derrickthomin/DJBB-Midi-Loopster/src/debug.py

import time
from collections import OrderedDict
from settings import SETTINGS

DEBUG_INTERVAL_S = 1.5  # Interval to print debug info (seconds)
DEBUG_MODE = SETTINGS["DEBUG"]

class Debug():
    """
    Debugging utility for displaying and managing debug information.

    Attributes:
        debug_header (str): Header text for the debug information.
        debug_dict (OrderedDict): Ordered dictionary to store debug data.
        debug_timer (float): Timer for managing debug printing intervals.
    """

    def __init__(self):
        """
        Initialize the Debug class.
        """
        self.debug_header = "Debug".center(50)
        self.debug_dict = OrderedDict()  # Stores everything to print
        self.debug_timer = time.monotonic()

    def check_display_debug(self):
        """
        Display and clear debug information if the interval has passed.
        """
        if time.monotonic() - self.debug_timer > DEBUG_INTERVAL_S:
            # Bail if nothing to display
            if not self.debug_dict:
                return

            print("")
            print(self.debug_header)
            print("_________".center(50))
            for key, item in self.debug_dict.items():
                print(f"{key}:  {item}")
            self.debug_dict = {}
            self.debug_timer = time.monotonic()

    def add_debug_line(self, title, data, instant=False):
        """
        Add a debug line with a title and data.

        Args:
            title (str): Title for the debug data.
            data (str): Debug data to display.
            instant (bool, optional): If True, instantly print the debug line. Defaults to False.
        """
        if not title or not data:
            return

        title = str(title)
        data = str(data)

        if instant:
            print(f"{title} : {data}")
        else:
            self.debug_dict[title] = data

# Create an instance of the Debug class for debugging
debug = Debug()
